Pillazo/Parallux/3MF Files/Panel Connector Right.3mf

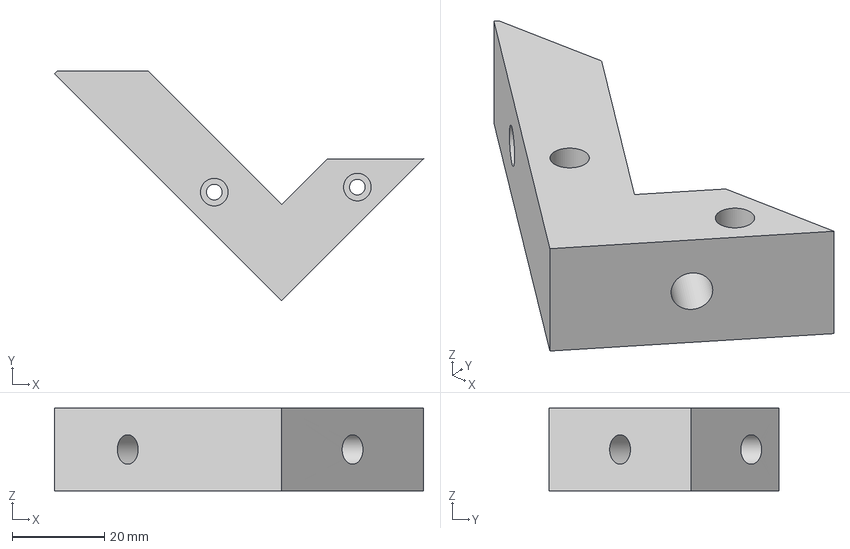
[picture p16: CAD file, 2026-02-09]
3MF Files/Panel Connector Right.3mf
80.2 x 49.9 x 18.0 mm
