Pillazo/Parallux/3MF Files/Pan Bearing Holder Front.3mf

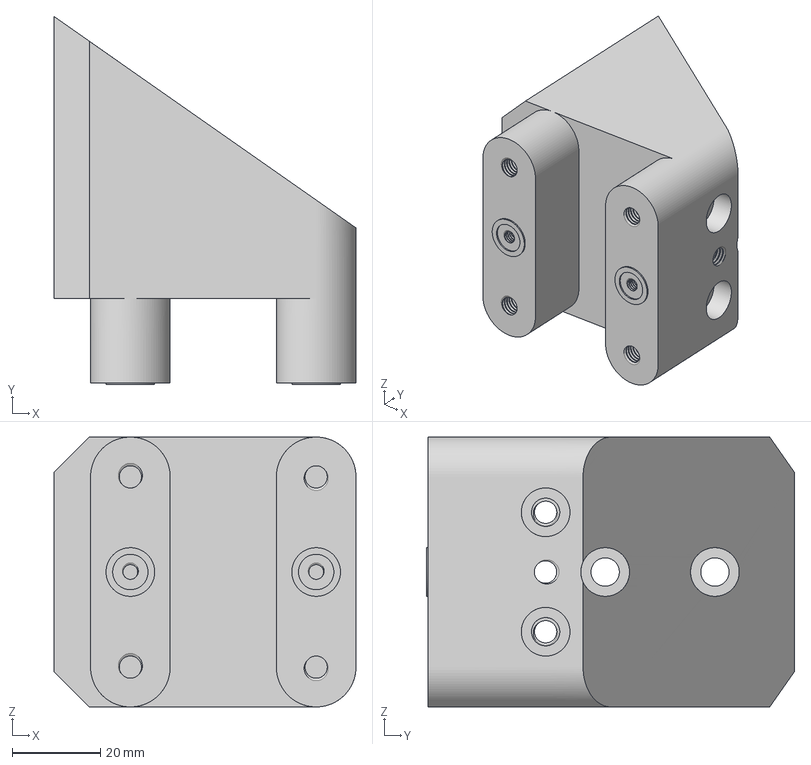
[picture p17: CAD file, 2026-02-09]
3MF Files/Pan Bearing Holder Front.3mf
68.3 x 83.2 x 61.0 mm
