Pillazo/Parallux/3MF Files/Motor Mount Adapter.3mf

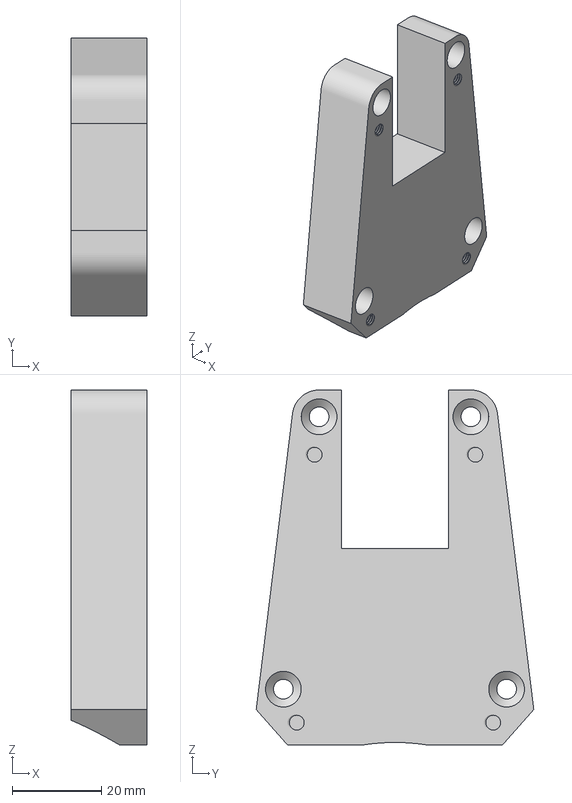
[picture p19: CAD file, 2026-02-09]
3MF Files/Motor Mount Adapter.3mf
17.1 x 62.2 x 79.5 mm
