Pillazo/Parallux/3MF Files/TiltCap.3mf

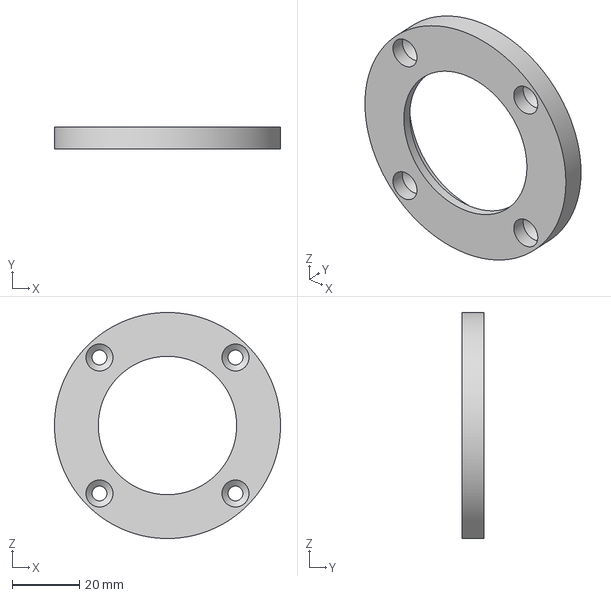
[picture p20: CAD file, 2026-02-09]
3MF Files/TiltCap.3mf
67.0 x 6.50 x 67.0 mm
