Pillazo/Parallux/3MF Files/Pan Gear Mount 2.3mf

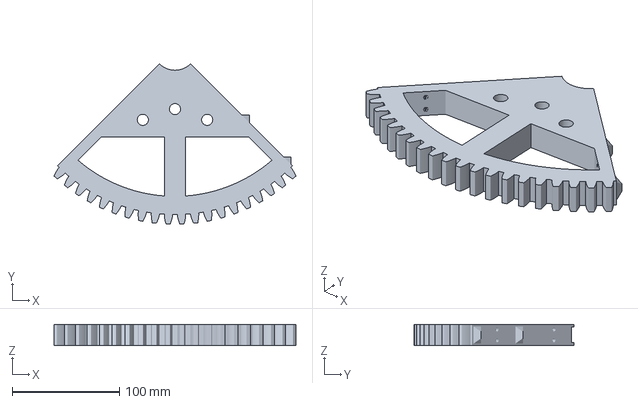
[picture p21: CAD file, 2026-02-09]
3MF Files/Pan Gear Mount 2.3mf
225.5 x 149.4 x 20.0 mm
