Pillazo/Parallux/3MF Files/Pan Base Mount.3mf

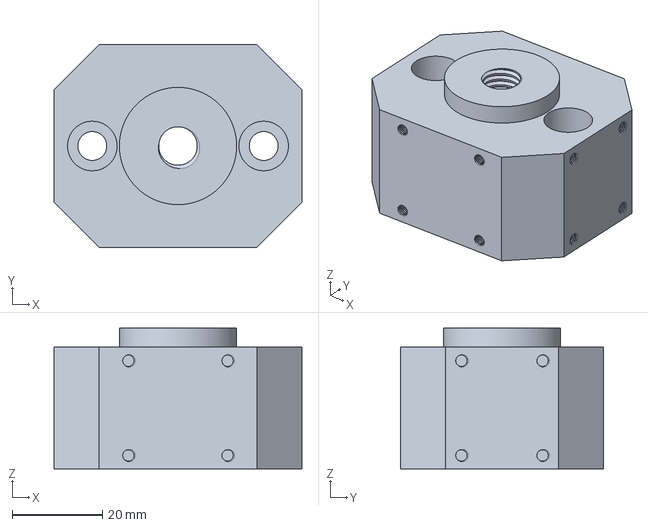
[picture p22: CAD file, 2026-02-09]
3MF Files/Pan Base Mount.3mf
55.0 x 45.0 x 31.3 mm
