Pillazo/Parallux/3MF Files/Tilt Upright 1 Upper.3mf

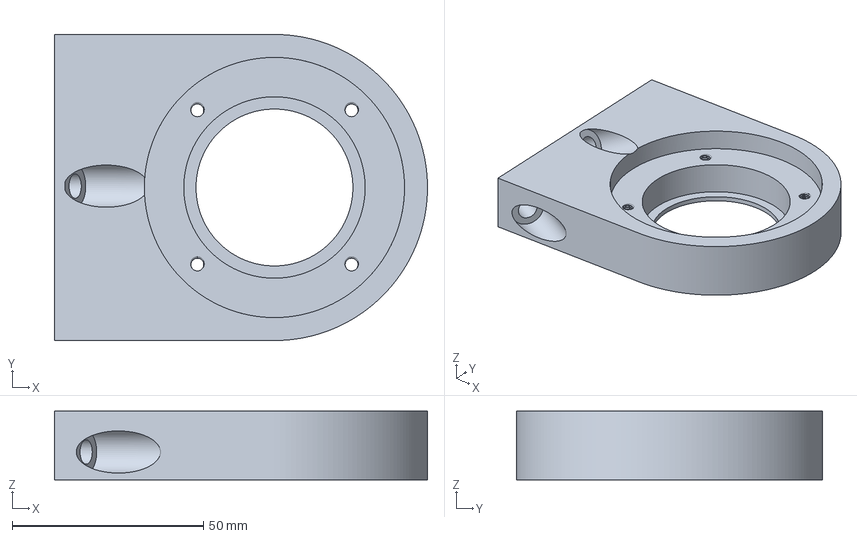
[picture p23: CAD file, 2026-02-09]
3MF Files/Tilt Upright 1 Upper.3mf
97.5 x 80.0 x 18.0 mm
