Pillazo/Parallux/3MF Files/Pan Bearing Cap.3mf

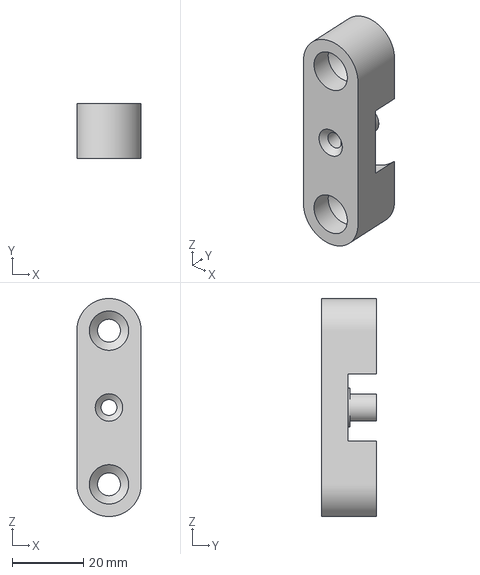
[picture p24: CAD file, 2026-02-09]
3MF Files/Pan Bearing Cap.3mf
18.0 x 15.5 x 61.0 mm
