Pillazo/Parallux/3MF Files/MirrorHolder.3mf

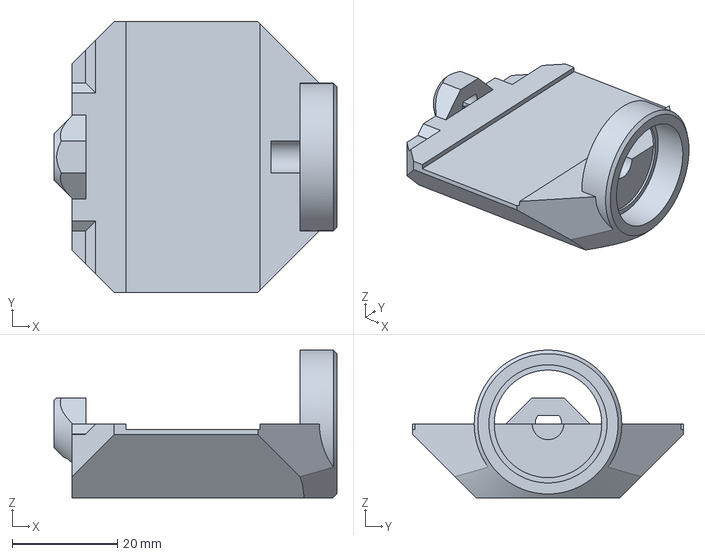
[picture p25: CAD file, 2026-02-09]
3MF Files/MirrorHolder.3mf
53.7 x 51.3 x 28.0 mm
