Pillazo/Parallux/3MF Files/PSCoverLower.3mf

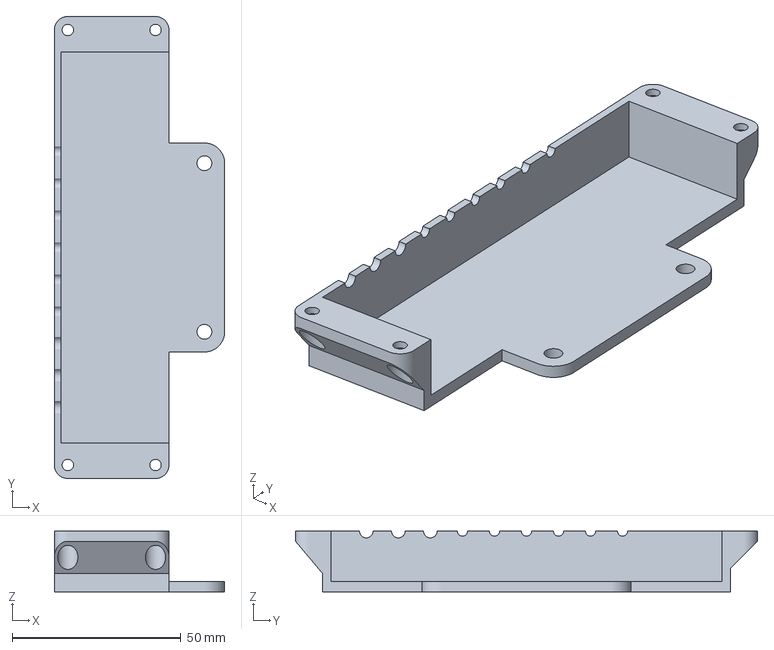
[picture p26: CAD file, 2026-02-09]
3MF Files/PSCoverLower.3mf
50.5 x 137.0 x 18.0 mm
