Pillazo/Parallux/3MF Files/DiscMount.3mf

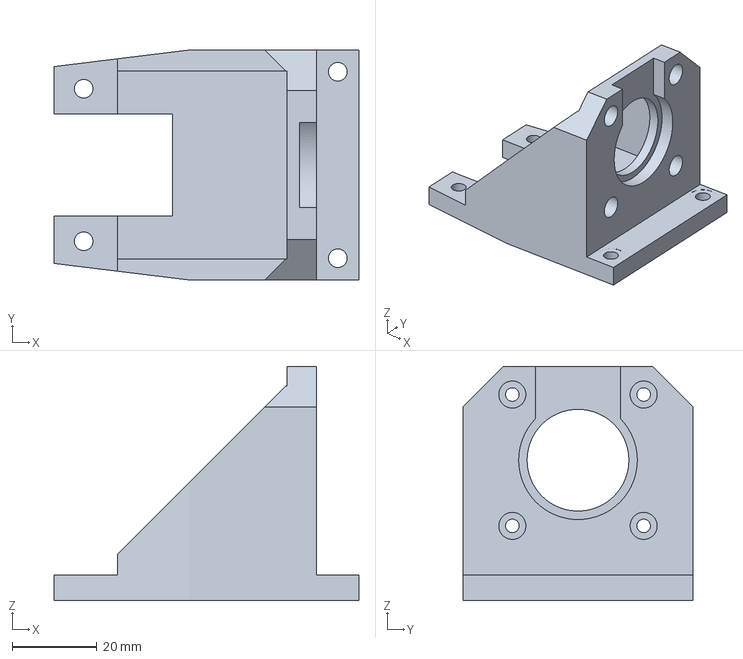
[picture p27: CAD file, 2026-02-09]
3MF Files/DiscMount.3mf
72.0 x 54.3 x 55.3 mm
