Pillazo/Parallux/3MF Files/EthernetLid.3mf

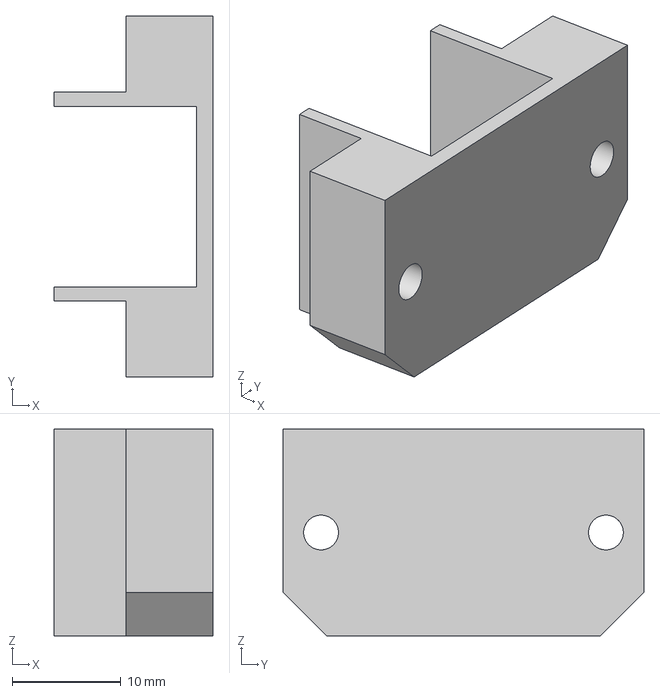
[picture p28: CAD file, 2026-02-09]
3MF Files/EthernetLid.3mf
14.6 x 33.2 x 19.0 mm
