Pillazo/Parallux/3MF Files/NaviFace.3mf

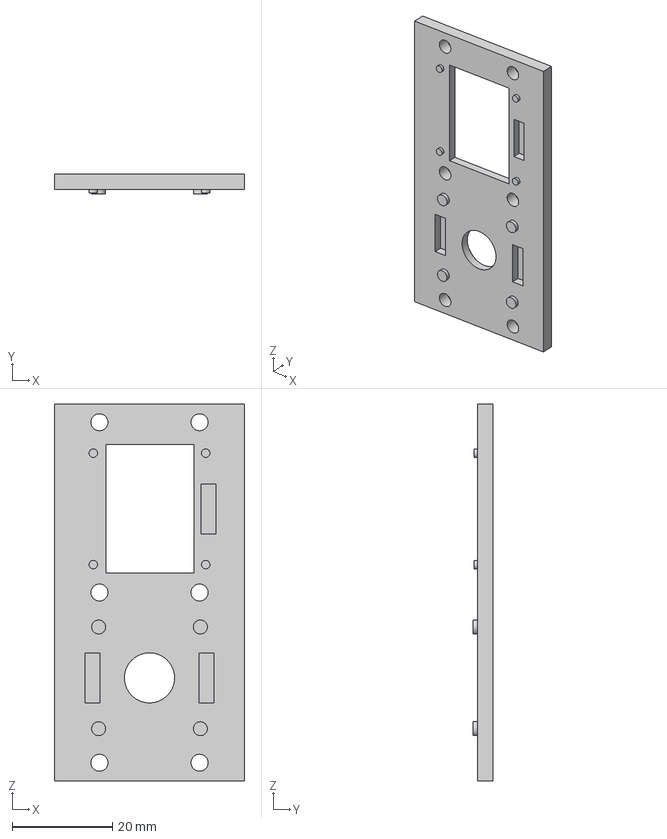
[picture p29: CAD file, 2026-02-09]
3MF Files/NaviFace.3mf
38.0 x 3.90 x 75.3 mm
