Pillazo/Parallux/3MF Files/Pan Motor Mount.3mf

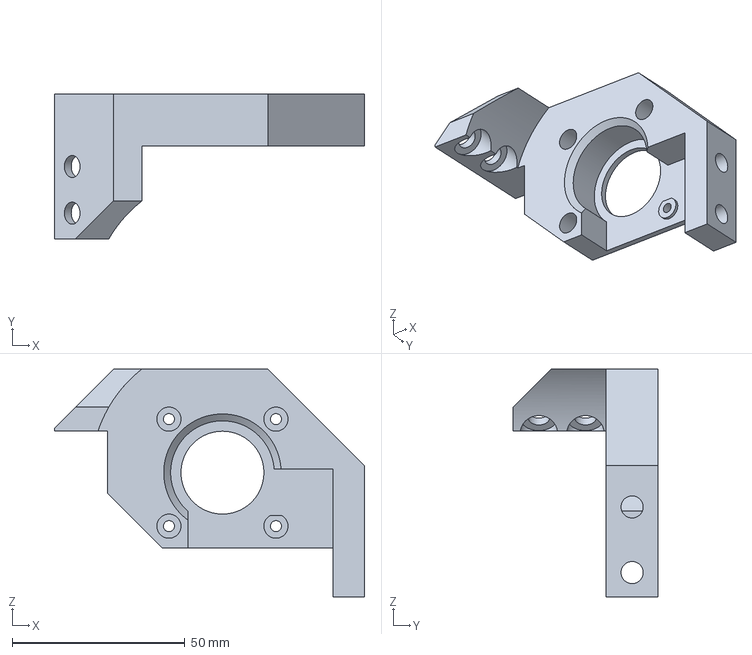
[picture p30: CAD file, 2026-02-09]
3MF Files/Pan Motor Mount.3mf
89.8 x 42.0 x 66.0 mm
