Pillazo/Parallux/3MF Files/Pan Bearing Holder Left.3mf

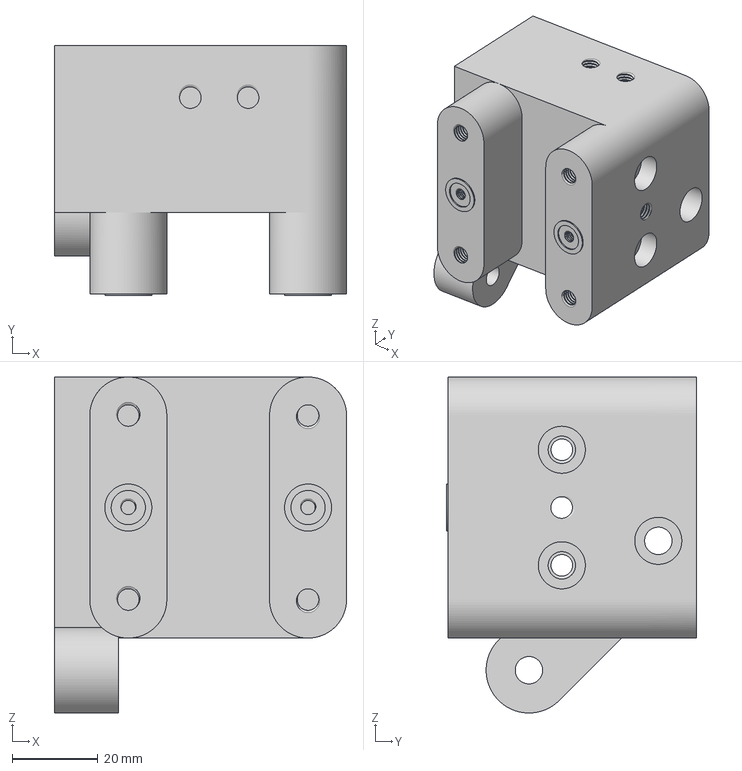
[picture p31: CAD file, 2026-02-09]
3MF Files/Pan Bearing Holder Left.3mf
68.3 x 58.4 x 78.5 mm
