Pillazo/Parallux/3MF Files/RearFrame.3mf

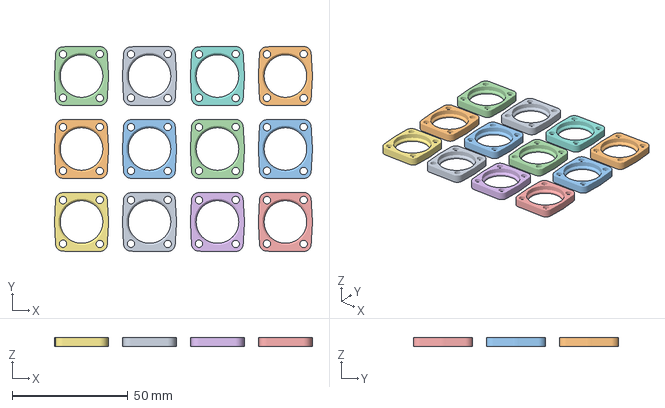
[picture p32: CAD file, 2026-02-09]
3MF Files/RearFrame.3mf
111.6 x 88.7 x 4.00 mm
