Pillazo/Parallux/3MF Files/Pipe Cap.3mf

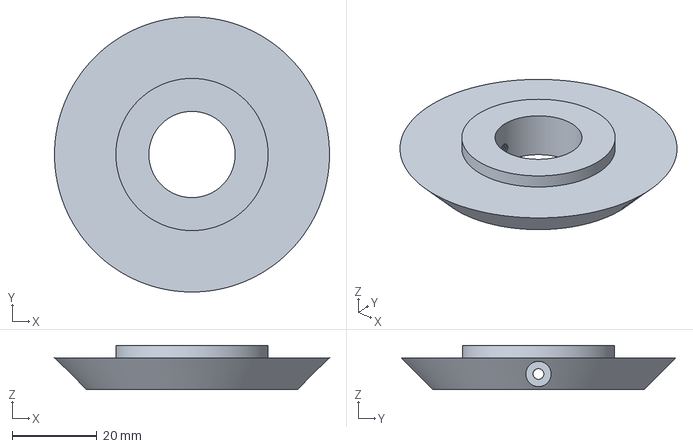
[picture p33: CAD file, 2026-02-09]
3MF Files/Pipe Cap.3mf
65.0 x 65.0 x 10.5 mm
