Pillazo/Parallux/3MF Files/PipeTool.3mf

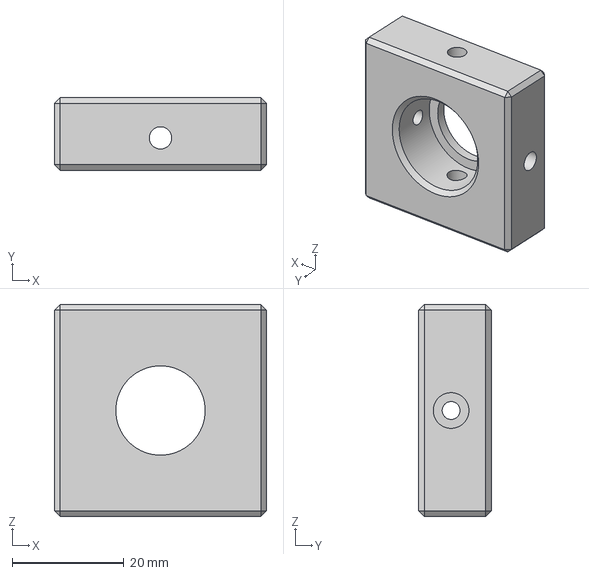
[picture p34: CAD file, 2026-02-09]
3MF Files/PipeTool.3mf
38.0 x 13.0 x 38.0 mm
