Pillazo/Parallux/3MF Files/Base Joiner Upper-PC.3mf

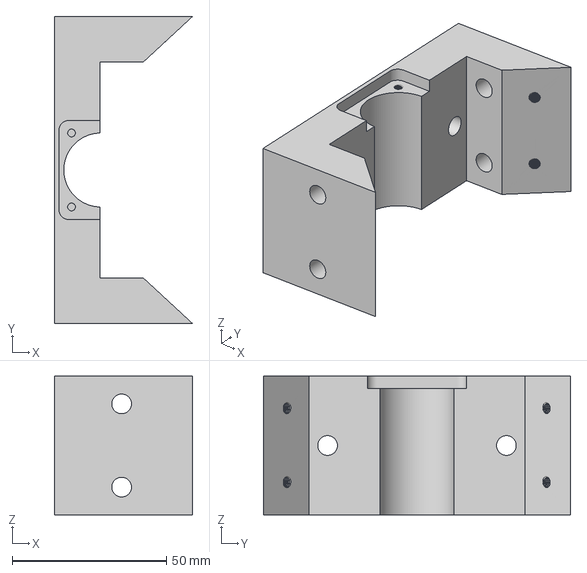
[picture p35: CAD file, 2026-02-09]
3MF Files/Base Joiner Upper-PC.3mf
44.8 x 99.6 x 45.0 mm
