Pillazo/Parallux/3MF Files/FacePlateStar.3mf

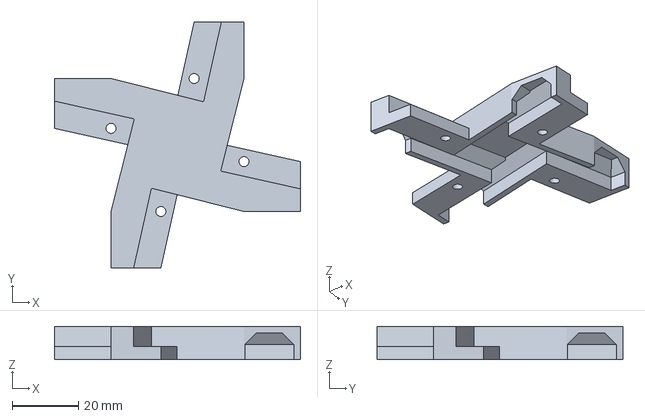
[picture p36: CAD file, 2026-02-09]
3MF Files/FacePlateStar.3mf
74.0 x 74.0 x 10.0 mm
