Pillazo/Parallux/3MF Files/Pan Bearing Holder Side.3mf

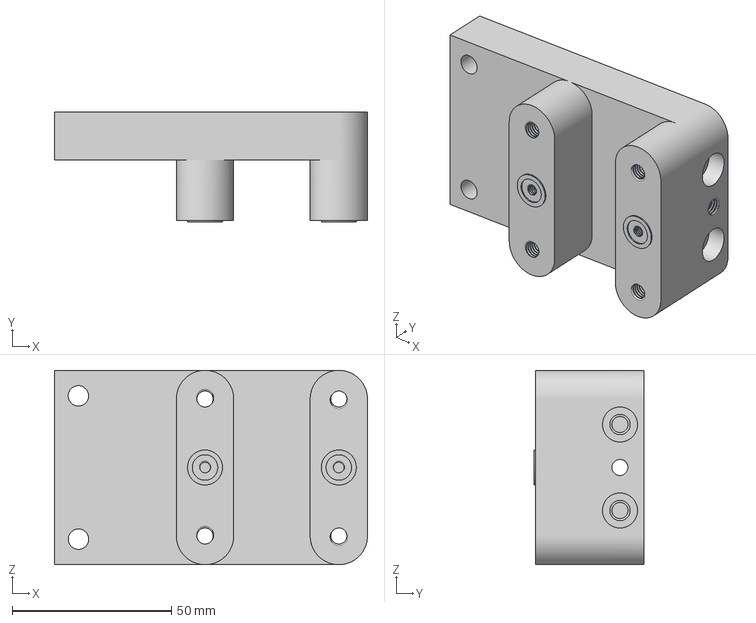
[picture p37: CAD file, 2026-02-09]
3MF Files/Pan Bearing Holder Side.3mf
98.3 x 34.4 x 61.0 mm
