Pillazo/Parallux/3MF Files/Bearing Cap.3mf

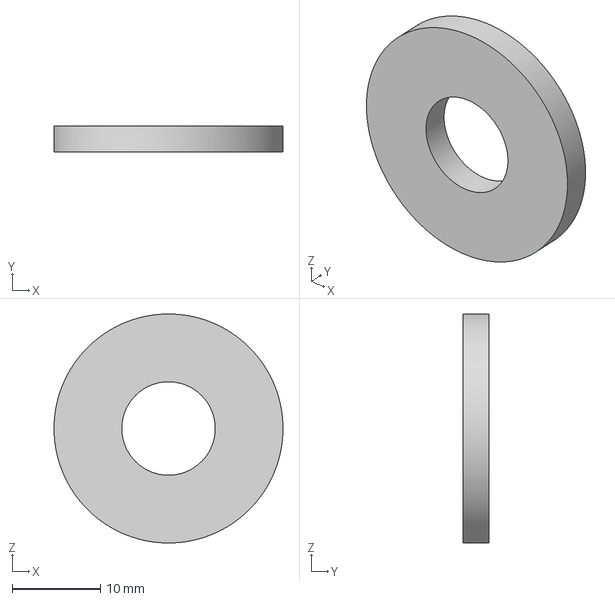
[picture p38: CAD file, 2026-02-09]
3MF Files/Bearing Cap.3mf
26.0 x 3.00 x 26.0 mm
