Pillazo/Parallux/3MF Files/CBShellHole.3mf

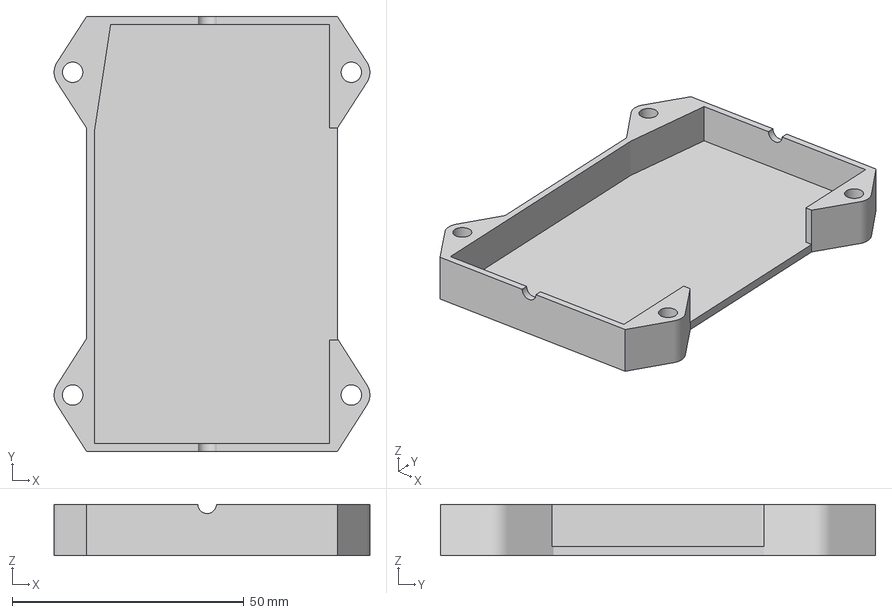
[picture p39: CAD file, 2026-02-09]
3MF Files/CBShellHole.3mf
68.1 x 93.8 x 11.1 mm
