Pillazo/Parallux/3MF Files/Pan Bearing Holder Right.3mf

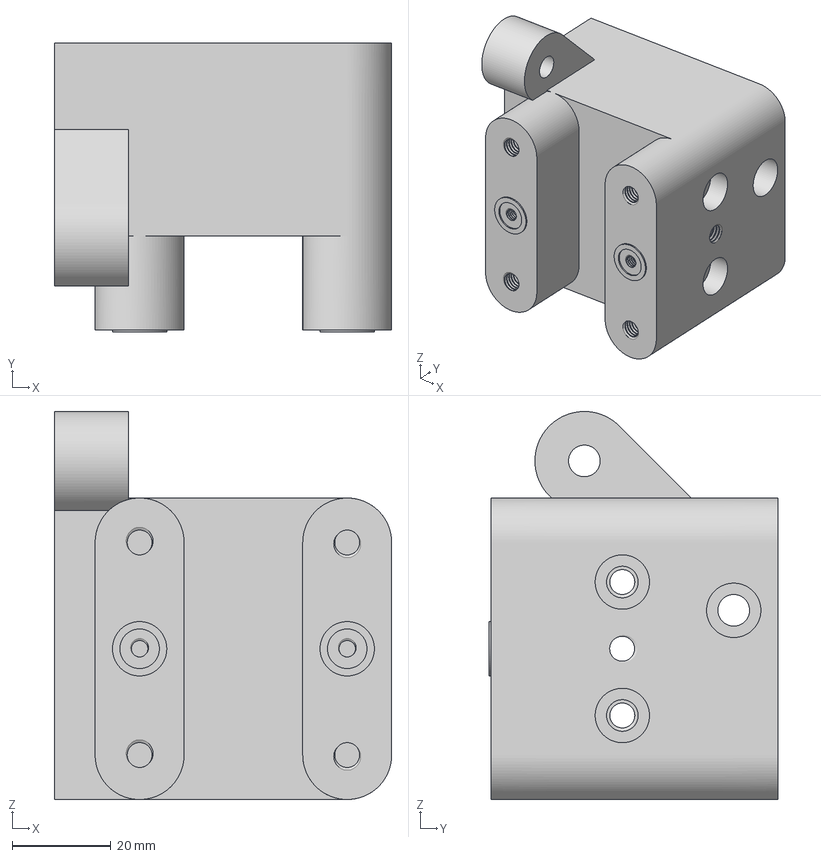
[picture p40: CAD file, 2026-02-09]
3MF Files/Pan Bearing Holder Right.3mf
68.3 x 58.4 x 78.5 mm
