Pillazo/Parallux/3MF Files/Ring Drive Gear.3mf

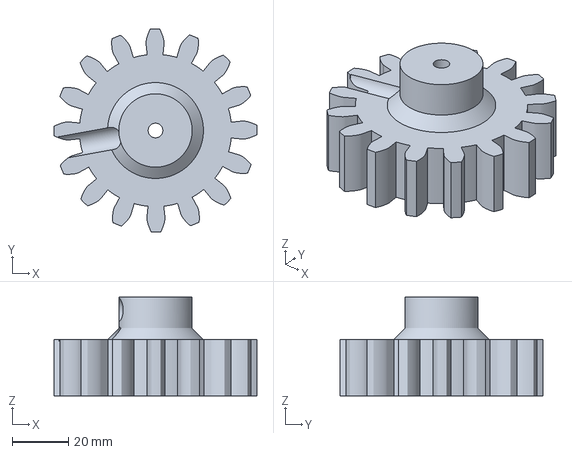
[picture p41: CAD file, 2026-02-09]
3MF Files/Ring Drive Gear.3mf
72.0 x 72.0 x 35.0 mm
