Pillazo/Parallux/3MF Files/Tilt Ring Small Gear Bearing.3mf

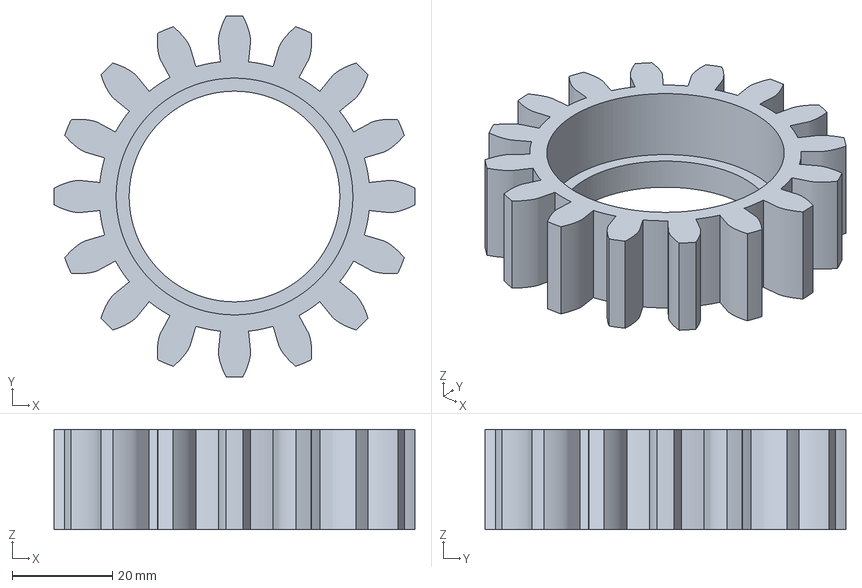
[picture p42: CAD file, 2026-02-09]
3MF Files/Tilt Ring Small Gear Bearing.3mf
72.0 x 72.0 x 20.0 mm
