Pillazo/Parallux/3MF Files/Motor Mount Offset 2.3mf

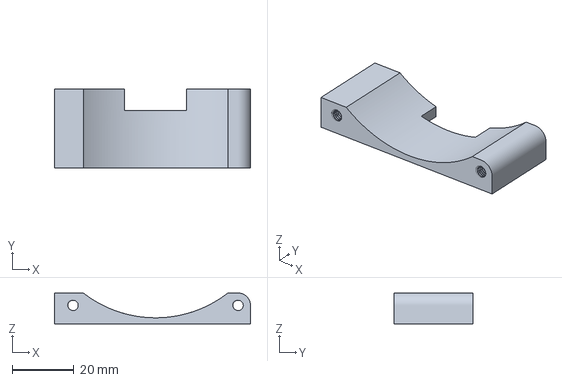
[picture p43: CAD file, 2026-02-09]
3MF Files/Motor Mount Offset 2.3mf
63.3 x 25.5 x 10.0 mm
