Pillazo/Parallux/3MF Files/WagoHolder Front.3mf

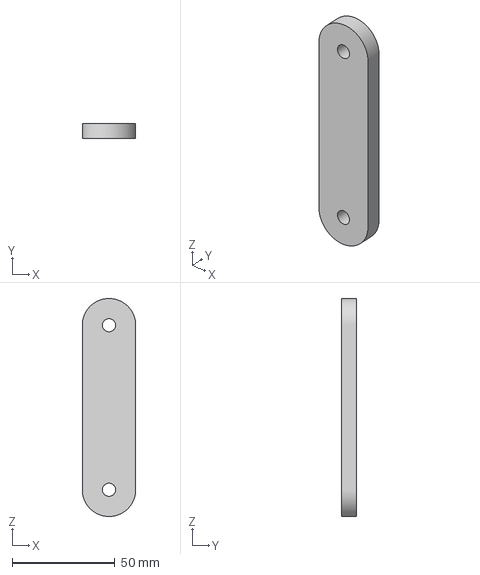
[picture p44: CAD file, 2026-02-09]
3MF Files/WagoHolder Front.3mf
26.0 x 7.50 x 106.0 mm
