Pillazo/Parallux/3MF Files/FrontFace.3mf

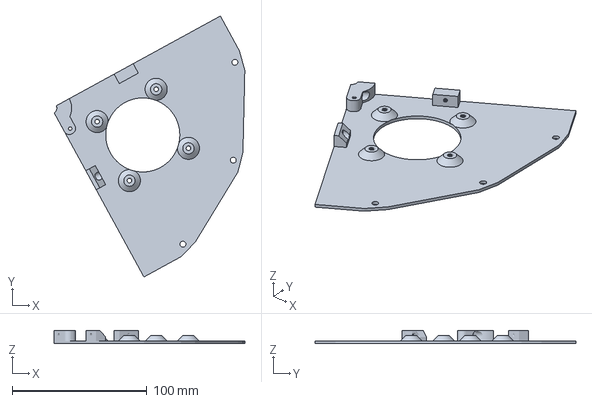
[picture p45: CAD file, 2026-02-09]
3MF Files/FrontFace.3mf
141.7 x 193.9 x 10.0 mm
