Pillazo/Parallux/3MF Files/Tilt Stopper.3mf

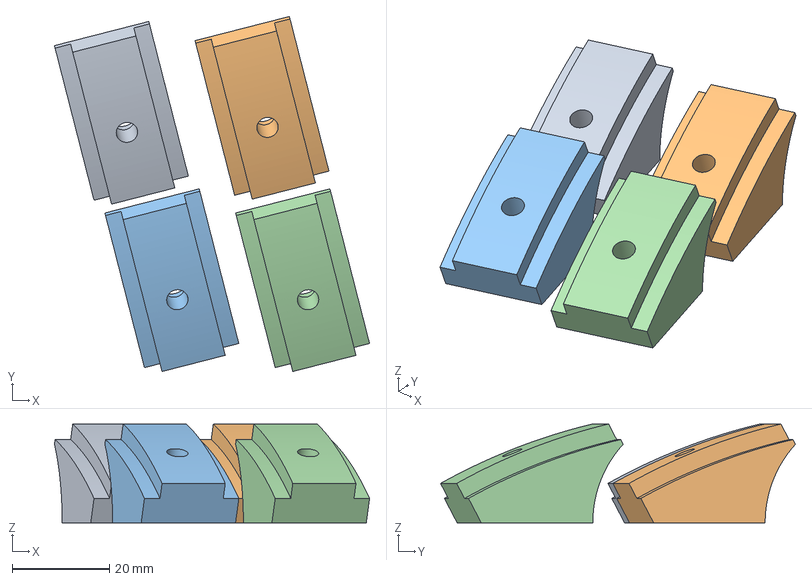
[picture p46: CAD file, 2026-02-09]
3MF Files/Tilt Stopper.3mf
64.7 x 72.9 x 20.3 mm
