Pillazo/Parallux/3MF Files/Disc Inner Gear.3mf

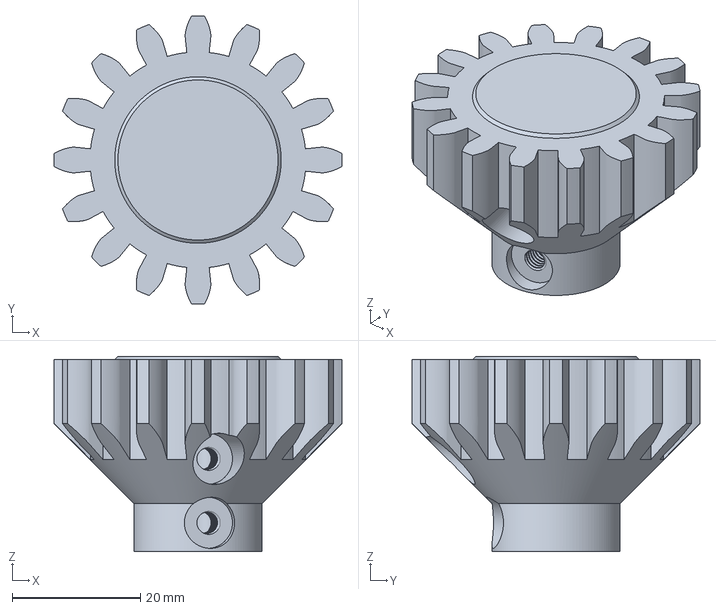
[picture p47: CAD file, 2026-02-09]
3MF Files/Disc Inner Gear.3mf
45.0 x 45.0 x 30.5 mm
