Pillazo/Parallux/3MF Files/PerfBase.3mf

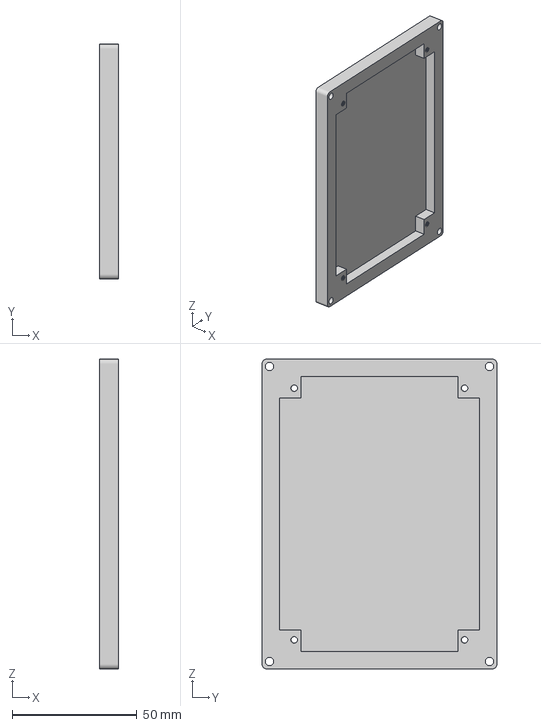
[picture p48: CAD file, 2026-02-09]
3MF Files/PerfBase.3mf
7.40 x 94.0 x 124.0 mm
