Pillazo/Parallux/3MF Files/Shim.3mf

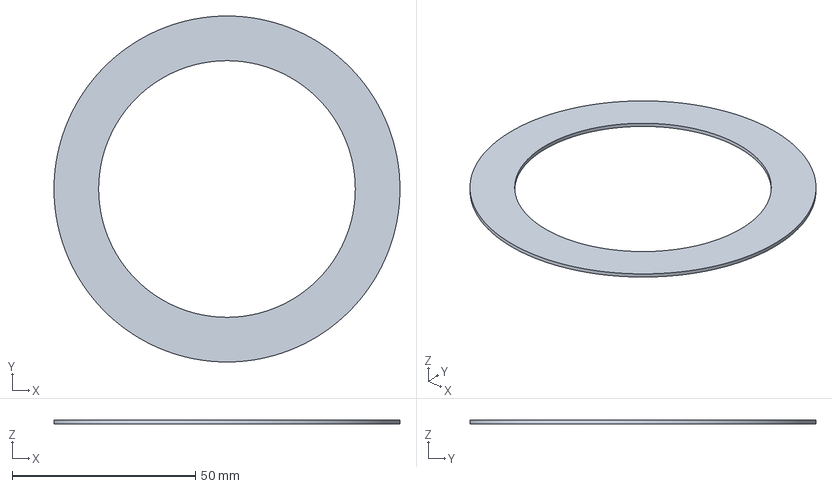
[picture p49: CAD file, 2026-02-09]
3MF Files/Shim.3mf
94.4 x 94.4 x 1.00 mm
