Pillazo/Parallux/3MF Files/Cable Chain.3mf

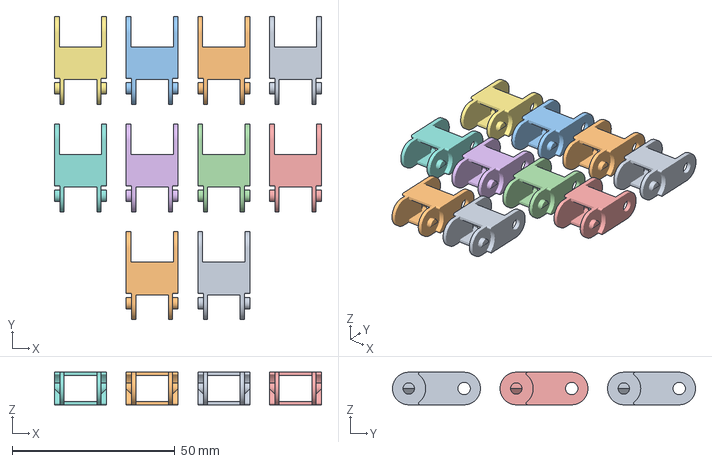
[picture p50: CAD file, 2026-02-09]
3MF Files/Cable Chain.3mf
82.0 x 93.0 x 10.0 mm
