Pillazo/Parallux/3MF Files/Pan Chain Attach Threads.3mf

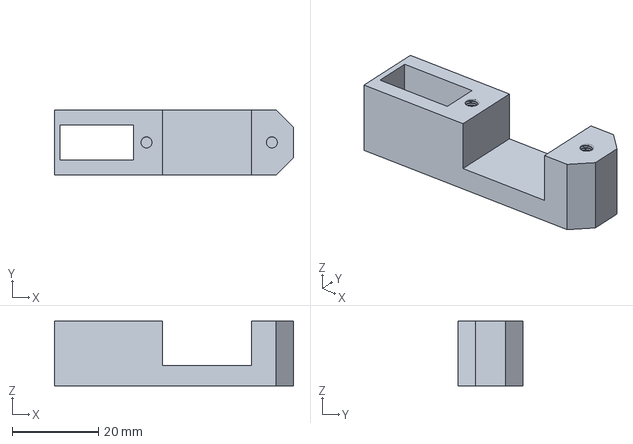
[picture p51: CAD file, 2026-02-09]
3MF Files/Pan Chain Attach Threads.3mf
55.3 x 15.0 x 15.0 mm
