Pillazo/Parallux/3MF Files/WireFixtureBottom2.3mf

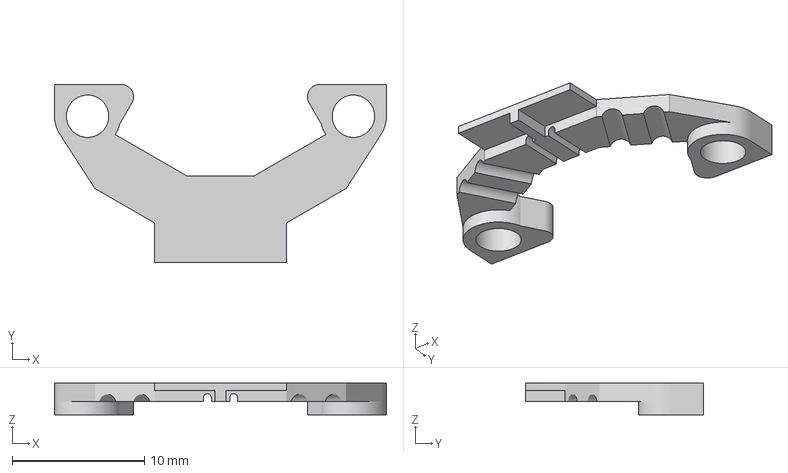
[picture p52: CAD file, 2026-02-09]
3MF Files/WireFixtureBottom2.3mf
25.1 x 13.5 x 2.40 mm
