Pillazo/Parallux/3MF Files/FrontLensCover.3mf

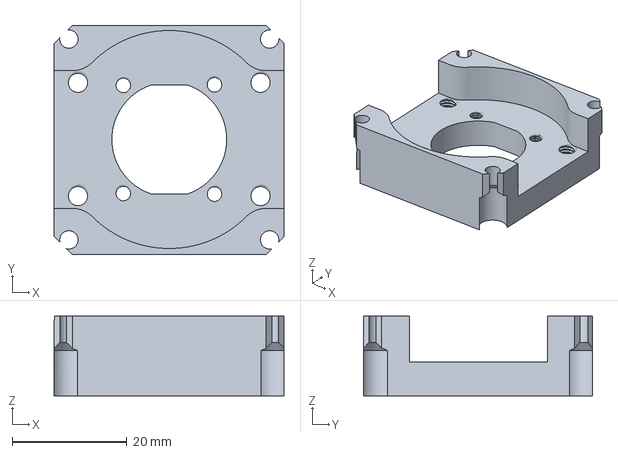
[picture p53: CAD file, 2026-02-09]
3MF Files/FrontLensCover.3mf
40.1 x 40.0 x 13.9 mm
