Pillazo/Parallux/3MF Files/RingSection.3mf

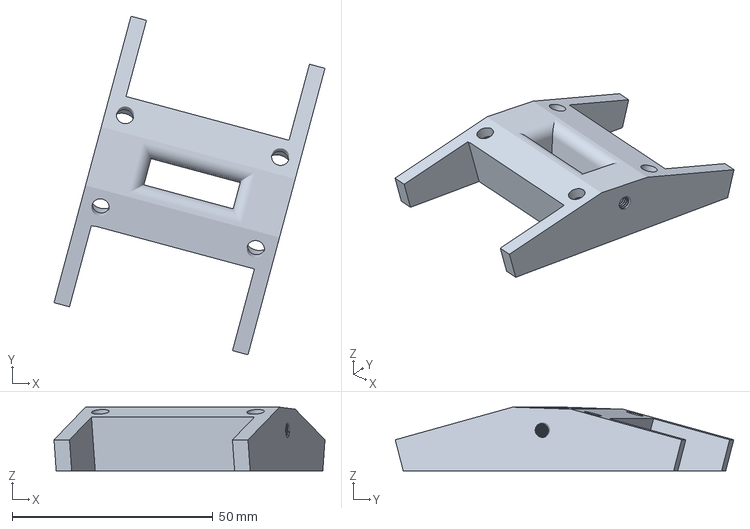
[picture p54: CAD file, 2026-02-09]
3MF Files/RingSection.3mf
67.5 x 84.3 x 15.9 mm
