Pillazo/Parallux/3MF Files/Tilt Motor Mount.3mf

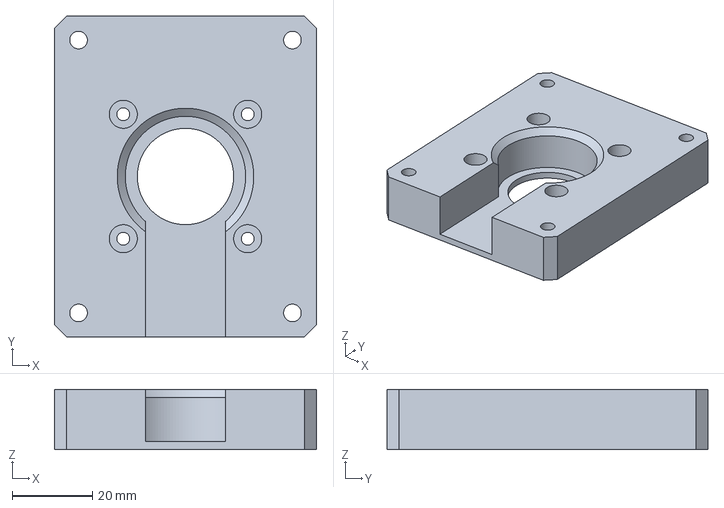
[picture p55: CAD file, 2026-02-09]
3MF Files/Tilt Motor Mount.3mf
65.3 x 80.0 x 15.0 mm
