Pillazo/Parallux/3MF Files/Pan Chain Attach Holes.3mf

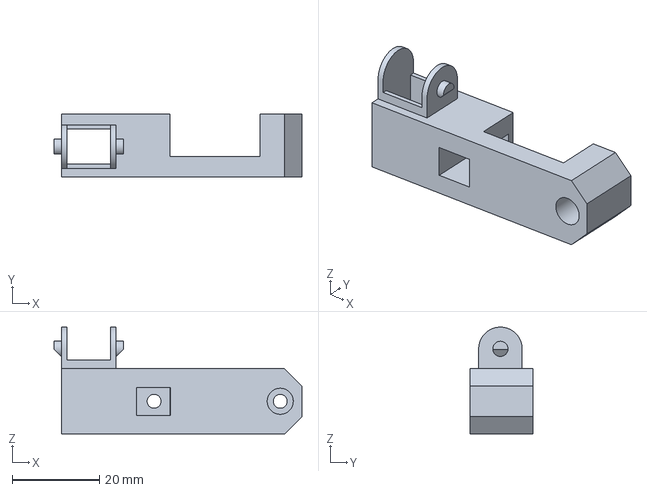
[picture p57: CAD file, 2026-02-09]
3MF Files/Pan Chain Attach Holes.3mf
57.0 x 14.5 x 24.6 mm
