Pillazo/Parallux/3MF Files/Fan Grill.3mf

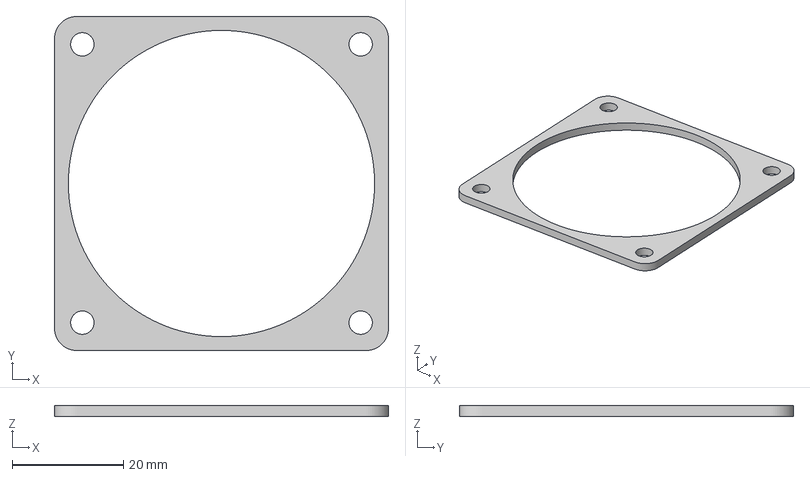
[picture p58: CAD file, 2026-02-09]
3MF Files/Fan Grill.3mf
60.0 x 60.0 x 2.00 mm
