Pillazo/Parallux/3MF Files/Wire Cap.3mf

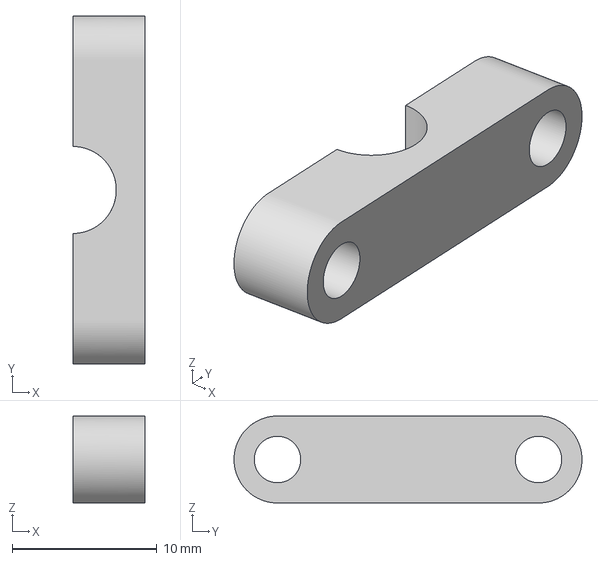
[picture p59: CAD file, 2026-02-09]
3MF Files/Wire Cap.3mf
5.00 x 24.0 x 6.00 mm
