Pillazo/Parallux/3MF Files/CBSheelThreads.3mf

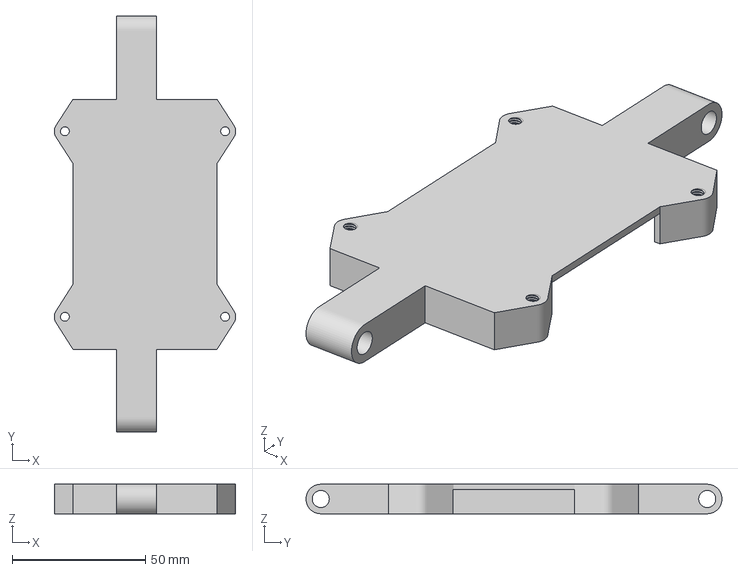
[picture p60: CAD file, 2026-02-09]
3MF Files/CBSheelThreads.3mf
68.1 x 156.1 x 11.1 mm
