Pillazo/Parallux/3MF Files/Tilt Gear 2.3mf

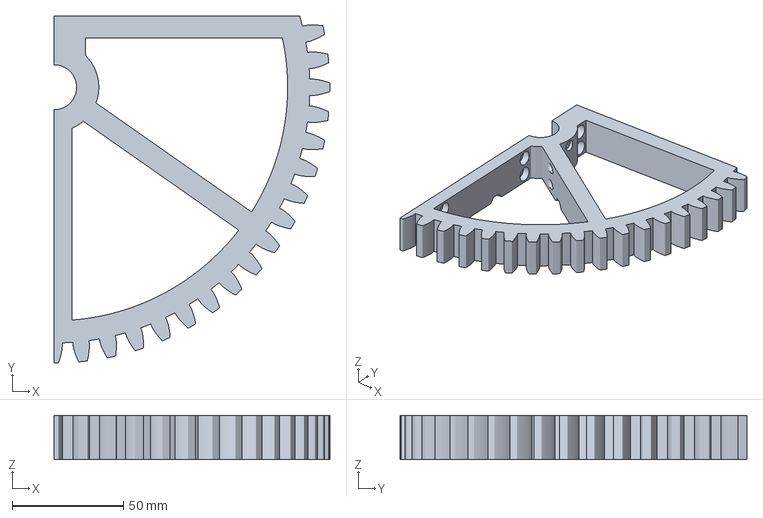
[picture p61: CAD file, 2026-02-09]
3MF Files/Tilt Gear 2.3mf
124.0 x 156.0 x 20.0 mm
