Pillazo/Parallux/3MF Files/WireFixtureTop.3mf

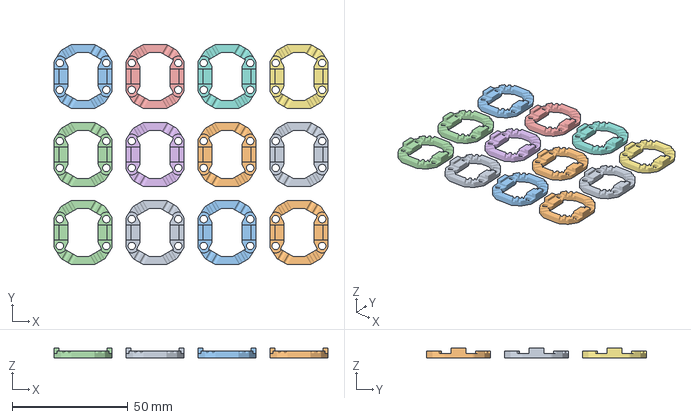
[picture p62: CAD file, 2026-02-09]
3MF Files/WireFixtureTop.3mf
118.4 x 95.1 x 4.40 mm
