Pillazo/Parallux/3MF Files/Wire Cap Front.3mf

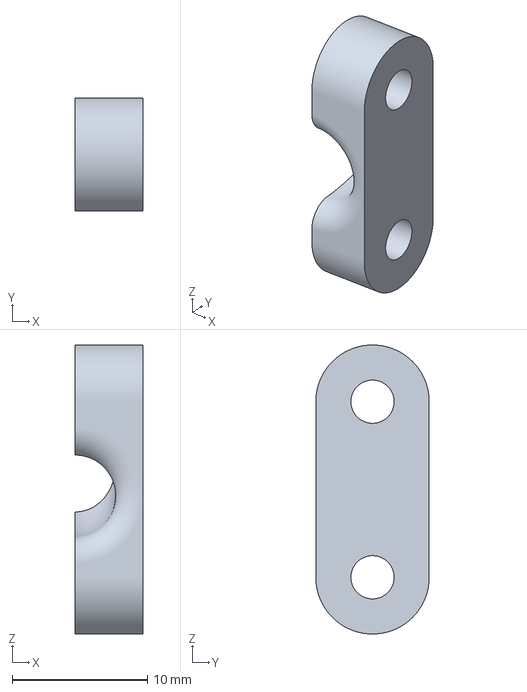
[picture p63: CAD file, 2026-02-09]
3MF Files/Wire Cap Front.3mf
5.00 x 8.40 x 21.4 mm
