Pillazo/Parallux/3MF Files/Electronics Lid.3mf

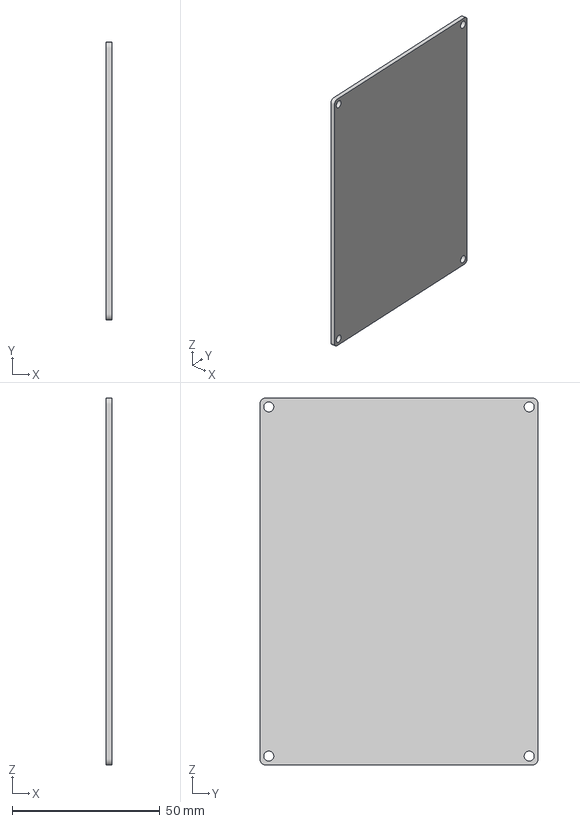
[picture p64: CAD file, 2026-02-09]
3MF Files/Electronics Lid.3mf
2.00 x 94.0 x 124.0 mm
