Pillazo/Parallux/3MF Files/PSCoverUpper.3mf

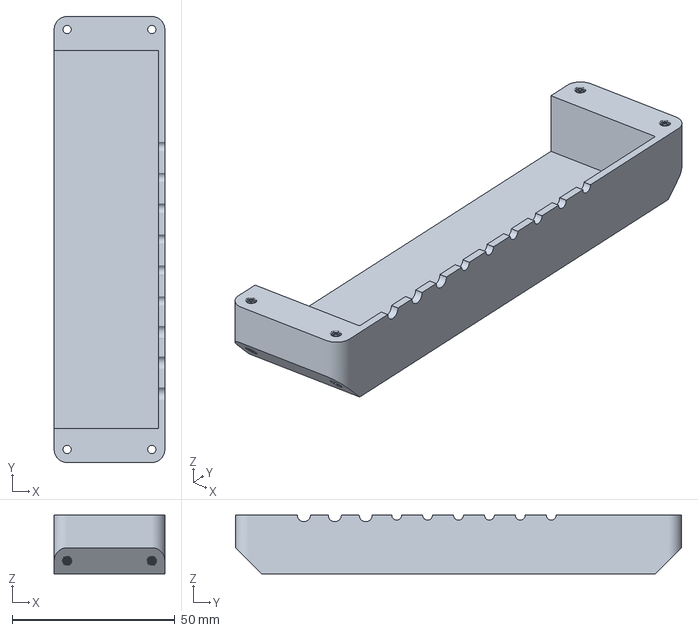
[picture p65: CAD file, 2026-02-09]
3MF Files/PSCoverUpper.3mf
34.0 x 137.0 x 18.0 mm
