Pillazo/Parallux/3MF Files/Tilt Gear Base Top.3mf

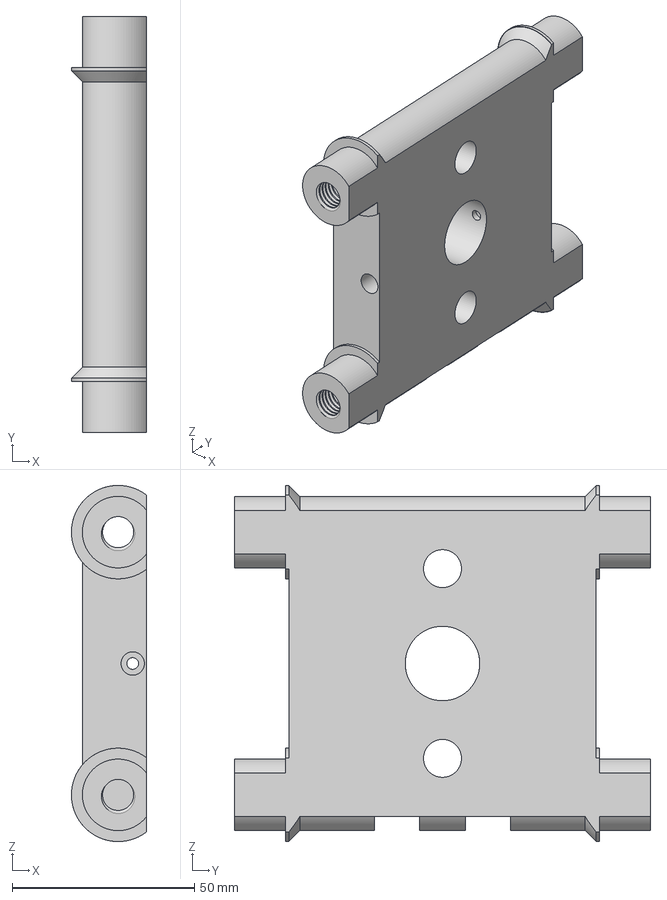
[picture p67: CAD file, 2026-02-09]
3MF Files/Tilt Gear Base Top.3mf
20.6 x 114.0 x 97.6 mm
