Pillazo/Parallux/3MF Files/NutToolLong.3mf

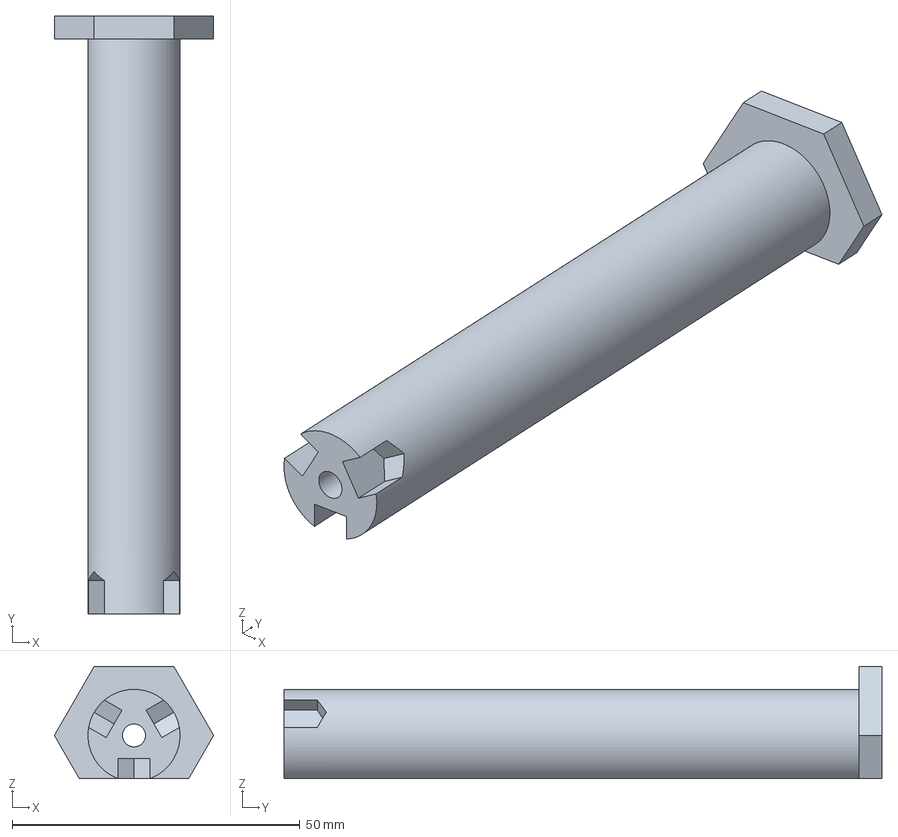
[picture p68: CAD file, 2026-02-09]
3MF Files/NutToolLong.3mf
27.7 x 104.0 x 19.5 mm
