Pillazo/Parallux/3MF Files/SlipRingTool.3mf

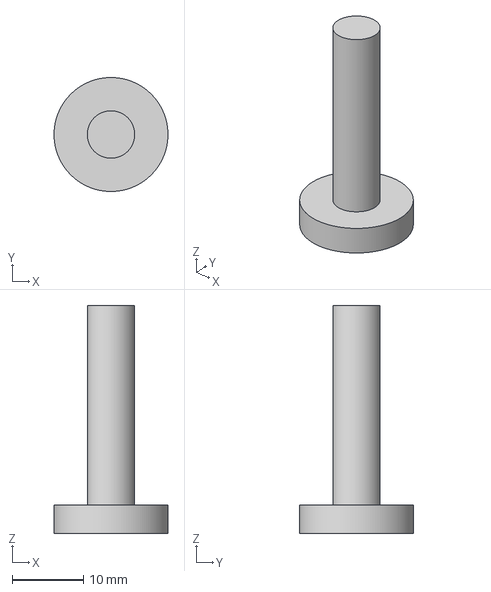
[picture p69: CAD file, 2026-02-09]
3MF Files/SlipRingTool.3mf
16.0 x 16.0 x 32.0 mm
