Pillazo/Parallux/3MF Files/Axel Key.3mf

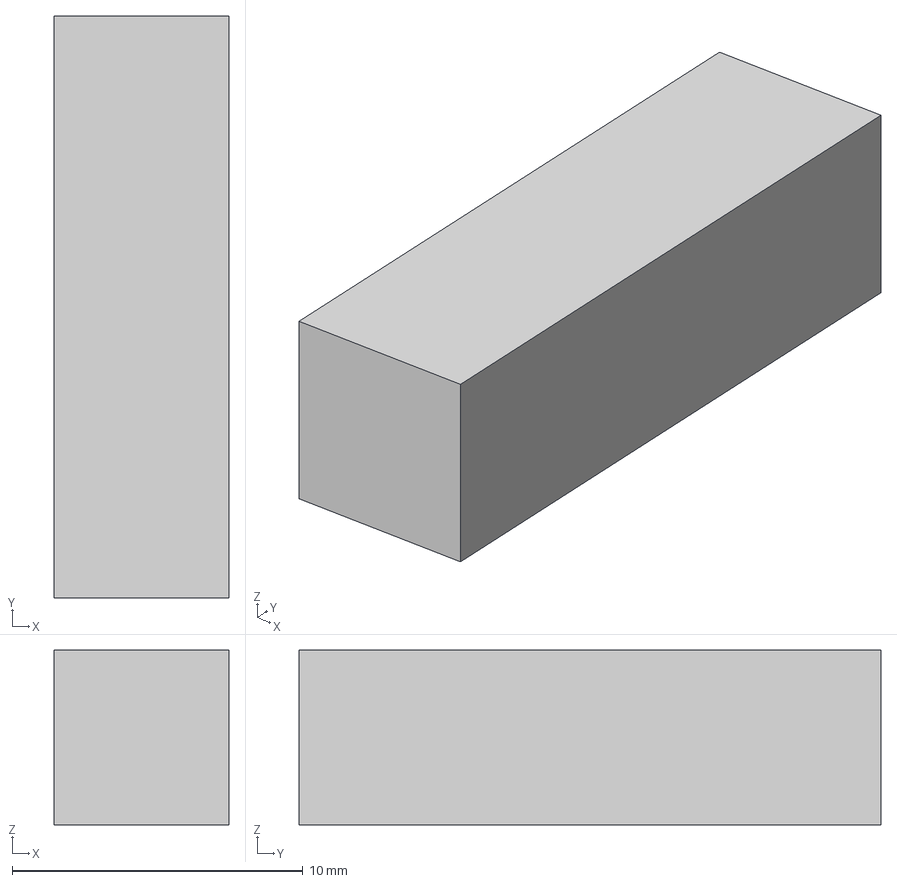
[picture p70: CAD file, 2026-02-09]
3MF Files/Axel Key.3mf
6.00 x 20.0 x 6.00 mm
