Pillazo/Parallux/3MF Files/Frame.3mf

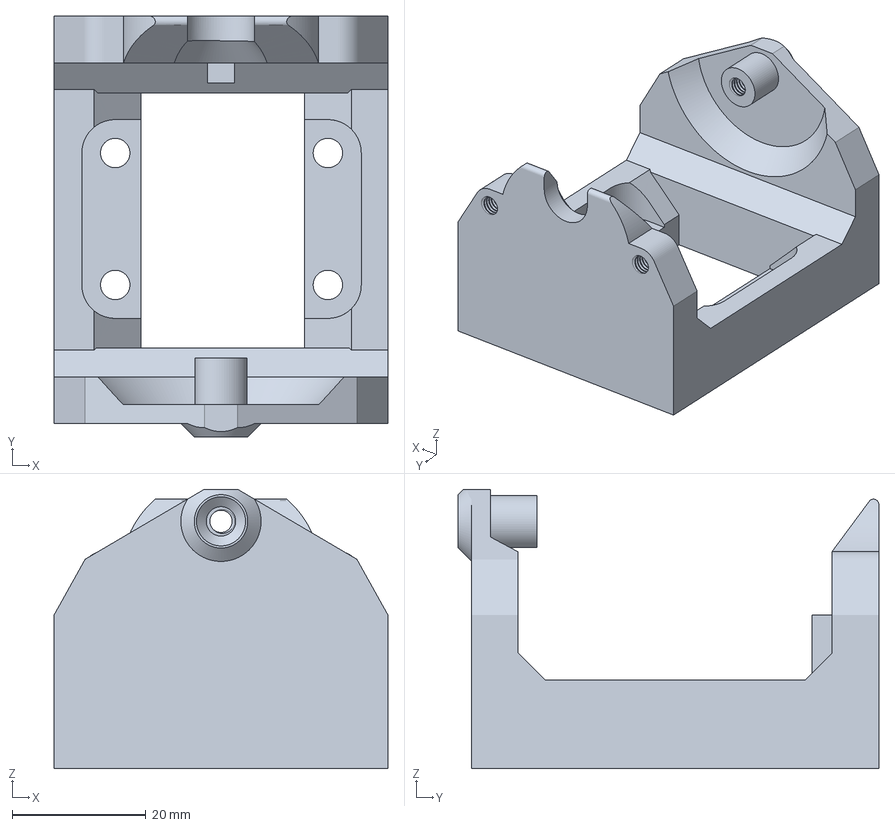
[picture p71: CAD file, 2026-02-09]
3MF Files/Frame.3mf
50.0 x 63.0 x 41.8 mm
