Pillazo/Parallux/3MF Files/Base Joiner Corner.3mf

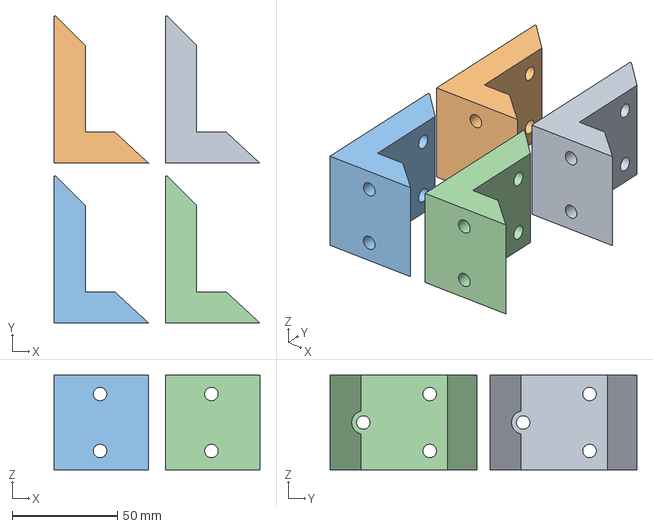
[picture p72: CAD file, 2026-02-09]
3MF Files/Base Joiner Corner.3mf
97.6 x 145.6 x 45.0 mm
