Pillazo/Parallux/3MF Files/Tilt Upright 1 Lower.3mf

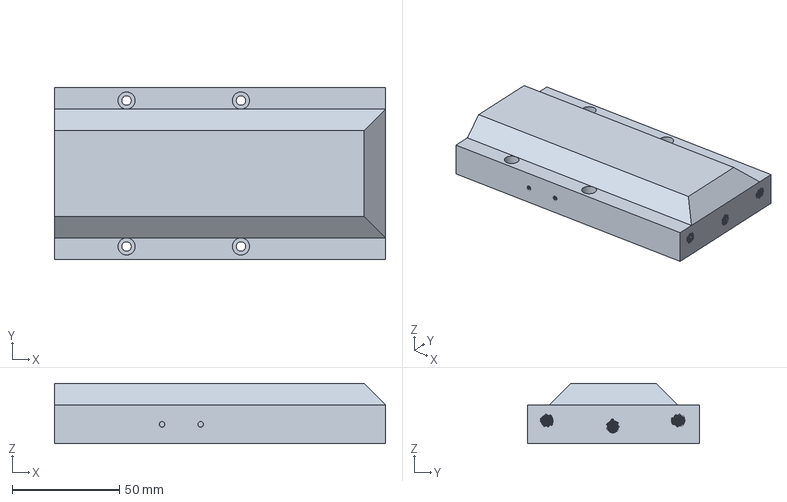
[picture p73: CAD file, 2026-02-09]
3MF Files/Tilt Upright 1 Lower.3mf
154.2 x 80.0 x 28.0 mm
