Pillazo/Parallux/3MF Files/PowerConMount.3mf

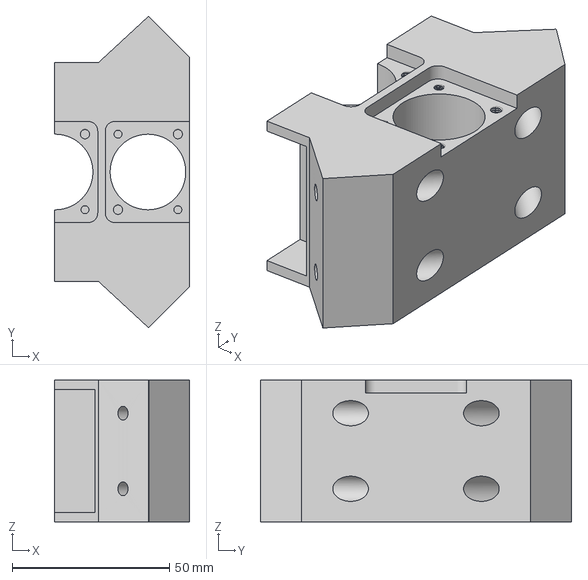
[picture p74: CAD file, 2026-02-09]
3MF Files/PowerConMount.3mf
43.0 x 98.8 x 45.0 mm
