Pillazo/Parallux/3MF Files/FrontFrame.3mf

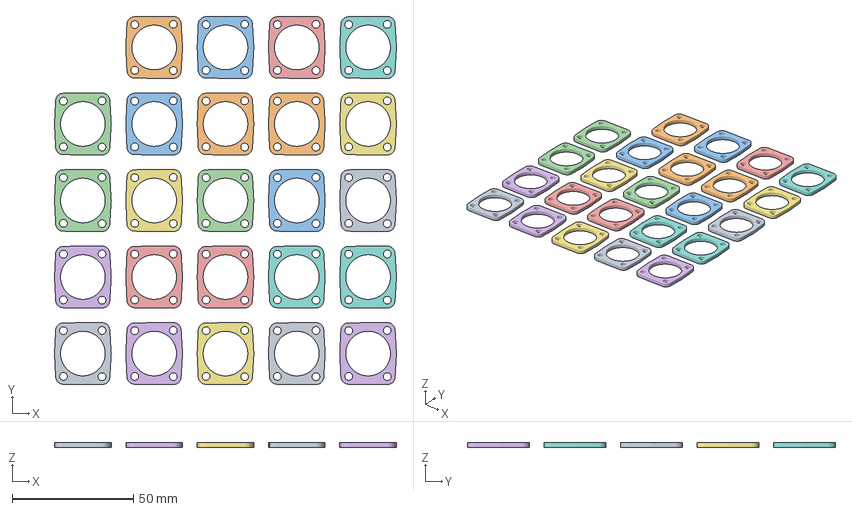
[picture p75: CAD file, 2026-02-09]
3MF Files/FrontFrame.3mf
141.0 x 151.8 x 2.00 mm
