Pillazo/Parallux/3MF Files/RingSectionDual.3mf

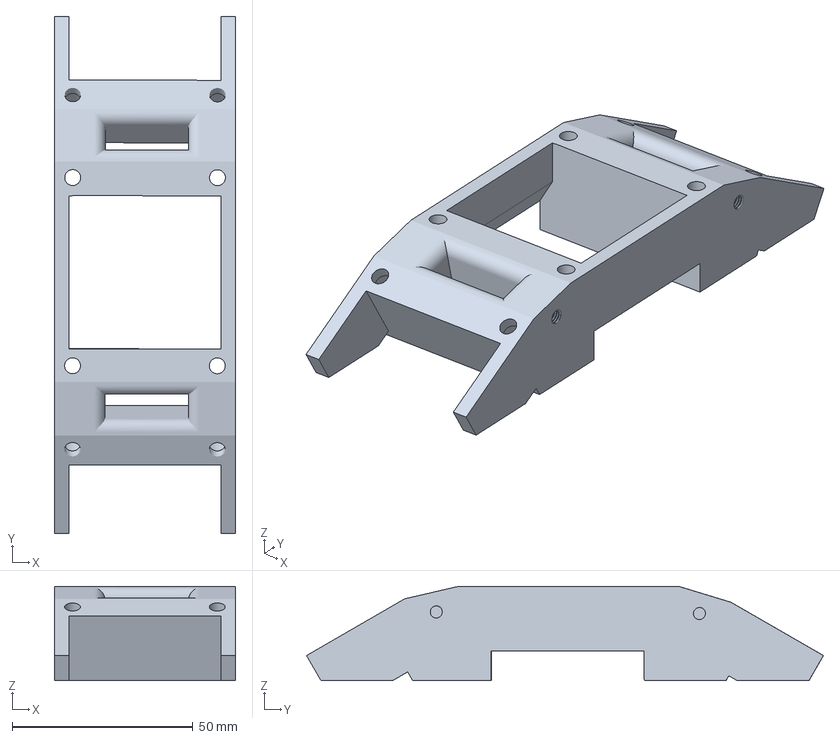
[picture p76: CAD file, 2026-02-09]
3MF Files/RingSectionDual.3mf
50.1 x 142.9 x 26.1 mm
