Pillazo/Parallux/3MF Files/Rubber Foot.3mf

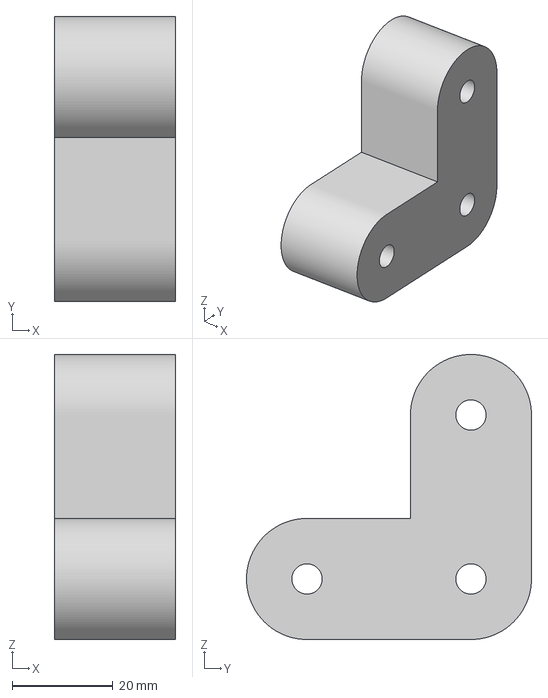
[picture p77: CAD file, 2026-02-09]
3MF Files/Rubber Foot.3mf
24.0 x 56.5 x 56.5 mm
