Pillazo/Parallux/3MF Files/Back Face.3mf

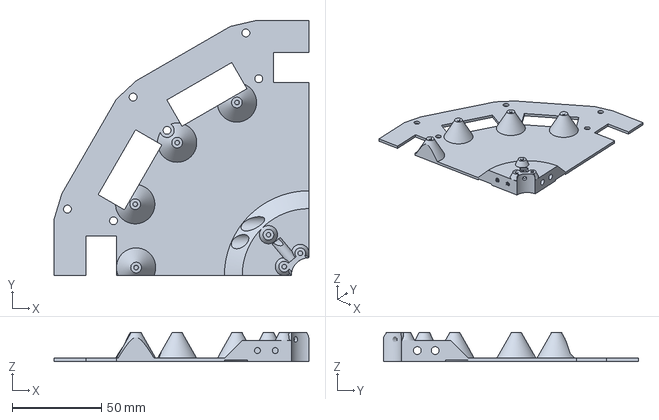
[picture p78: CAD file, 2026-02-09]
3MF Files/Back Face.3mf
142.9 x 143.0 x 16.5 mm
