Pillazo/Parallux/3MF Files/Pan Center.3mf

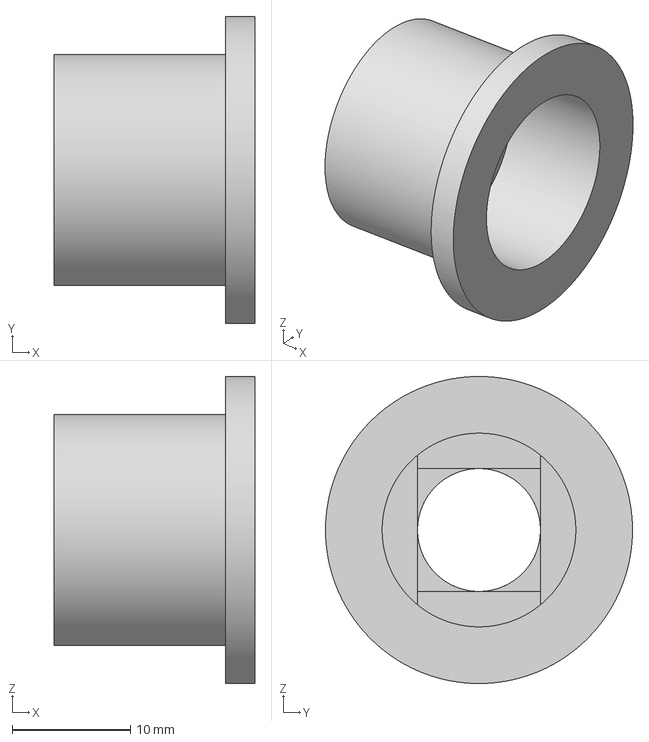
[picture p79: CAD file, 2026-02-09]
3MF Files/Pan Center.3mf
17.0 x 26.0 x 26.0 mm
