Pillazo/Parallux/3MF Files/Base Joiner Upper.3mf

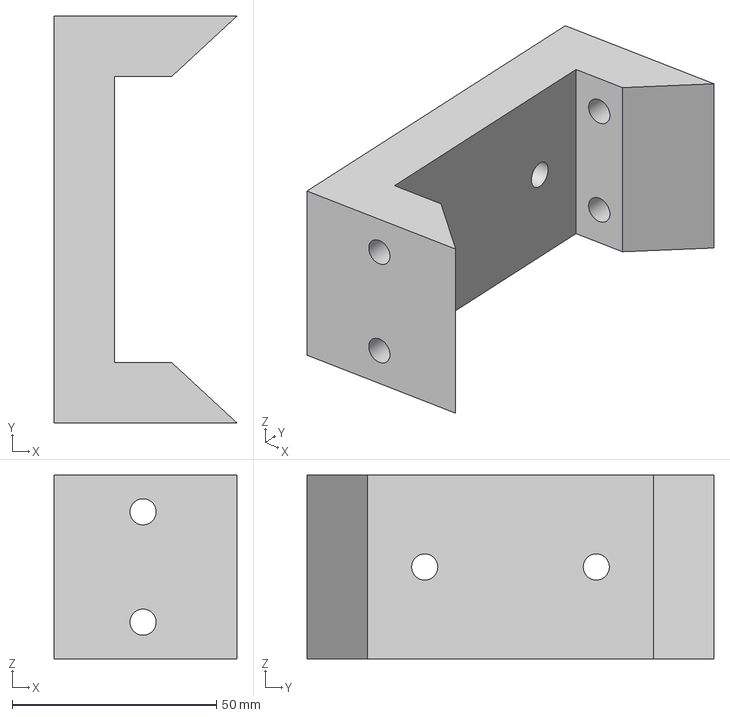
[picture p80: CAD file, 2026-02-09]
3MF Files/Base Joiner Upper.3mf
44.8 x 99.6 x 45.0 mm
