Pillazo/Parallux/3MF Files/Cable Chain Base.3mf

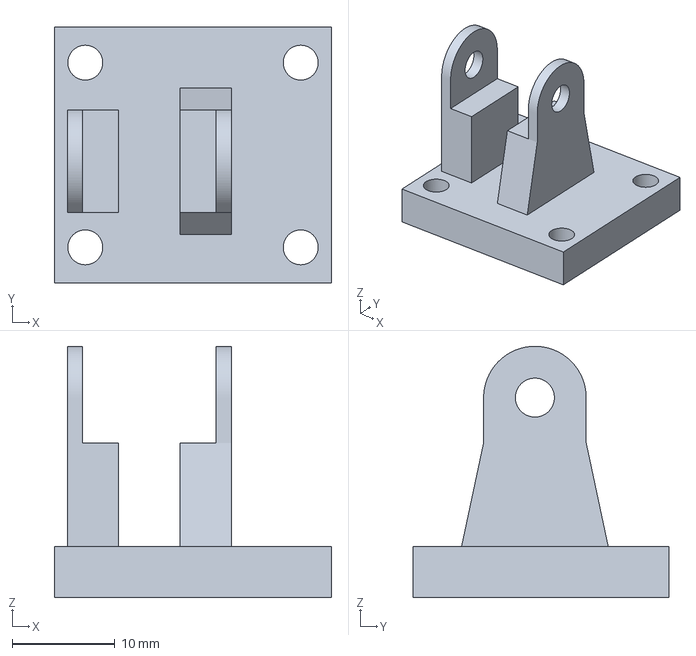
[picture p81: CAD file, 2026-02-09]
3MF Files/Cable Chain Base.3mf
27.0 x 25.0 x 24.5 mm
