Pillazo/Parallux/3MF Files/Base Joiner Lower.3mf

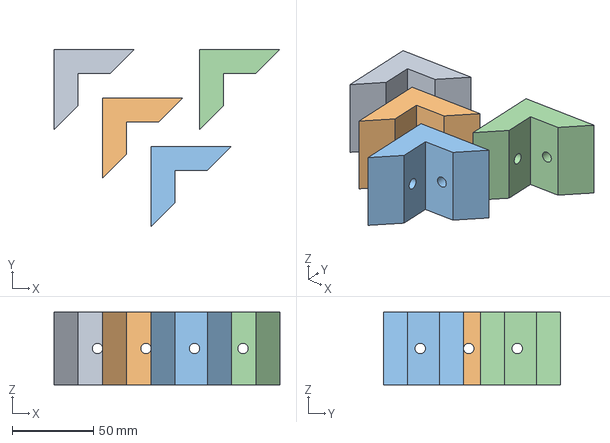
[picture p82: CAD file, 2026-02-09]
3MF Files/Base Joiner Lower.3mf
139.4 x 109.4 x 45.0 mm
